BrettHallen/Apogee-BK_01/Apogee-BK_01_Power/Apogee-BK_01_Power_3D.png

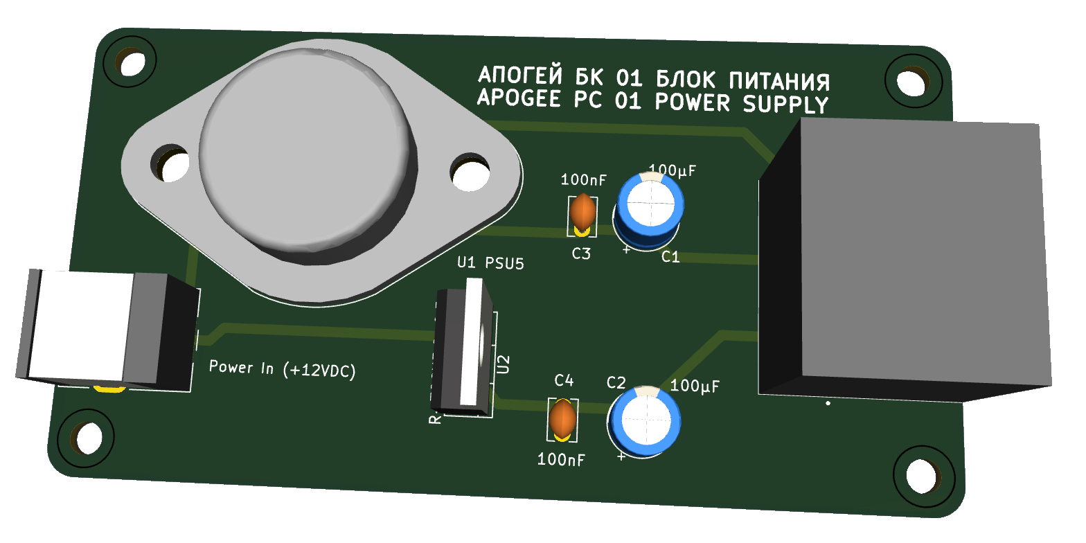
Apogee-BK_01_Power/Apogee-BK_01_Power_3D.png
