BrettHallen/Apogee-BK_01/Schematics/Apogee_BK01_Schematic4.jpg

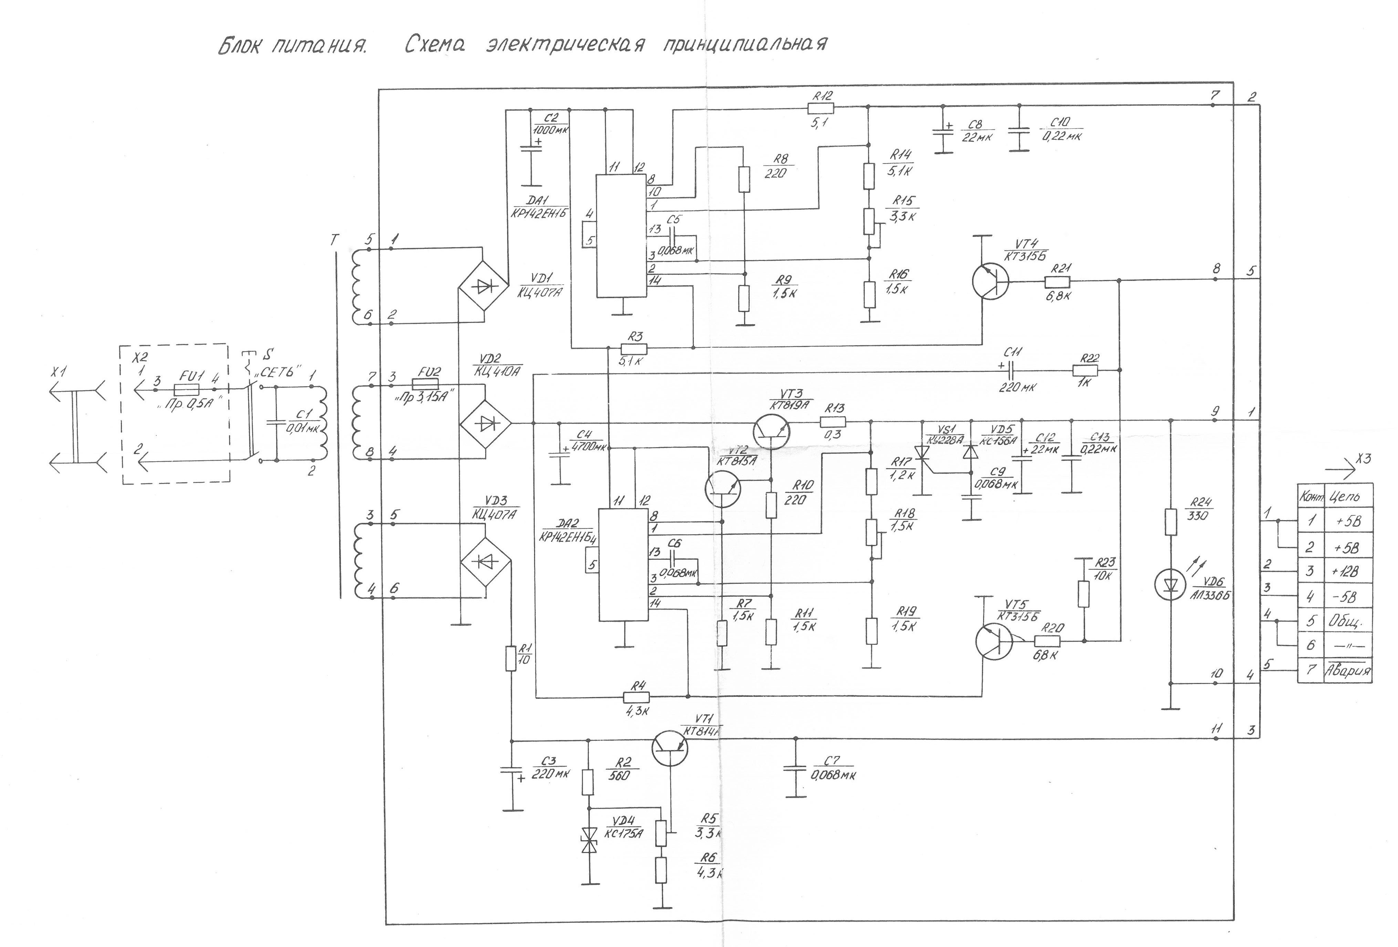
Schematics/Apogee_BK01_Schematic4.jpg
